Molly-M-Laugh/Senior-Final/Hardware/Final Circuits/sd_pcm.pdf

Choosing a Protection Circuit Module for a One-Cell Lithium Iron Phosphate Battery For this project, I am using a one-cell lithium iron phosphate battery, so I am choosing a protection circuit module (often called a protection board) instead of a full battery management system. I chose a protection circuit module because a one-cell battery does not need cell balancing, which is one of the main functions of a larger battery management system used in multi-cell battery packs. In many online listings, sellers still call one-cell protection boards “battery management systems,” but for my design the more accurate term is protection circuit module.
A protection circuit module is the board that sits between the battery and the rest of the system and protects the battery during unsafe conditions, such as overcharging, over-discharging, over-current, and short circuits.

What I need to check when choosing a protection circuit module
1) It must match the battery chemistry and cell count
The most important thing is that the board must be made for a one-cell lithium iron phosphate battery. This is usually written as 1S LiFePO4.
This must be checked first because lithium iron phosphate batteries use different voltage limits than regular lithium-ion or lithium-polymer batteries.
When looking at the datasheets, look for wording like:
- 1S LiFePO4
- one-cell lithium iron phosphate protection board
- LiFePO4 protection circuit module
2) The continuous discharge current rating must be high enough
The protection circuit module has a continuous discharge current rating, which determines how much current it can safely pass during normal operation without overheating or tripping.
This matters because the system will draw current from the battery through this board, and the board must be able to handle that current comfortably. Even though my first-pass estimate for peak battery current is around the 1 amp range, I should still choose a board with margin because startup behavior, converter bursts, and real-world conditions can cause temporary increases.
For my prototype, a practical choice is:
- at least 3 amps continuous discharge current
- 5 amps continuous is even better because it gives extra margin and reduces the chance of nuisance trips
3) Check the over-current protection behavior
Besides the continuous rating, the board usually has an over-current protection threshold, which is the current level where it decides something is wrong and shuts off or trips protection.
This value is important because I do not want the board to trip during normal system operation, but I do want it to trip if there is a real fault. If the threshold is too low, the system may randomly shut off during startup or current bursts. If the threshold is too high, the protection may be less effective.
I should also check whether the listing mentions short-circuit protection, since that is another major job of the protection circuit module.
4) The charge current rating must support the charger
Even though my design will not charge while running, the protection circuit module still has to handle charging current when I do charge the battery.
I need to check the board’s maximum charge current and make sure it is at least as high as the charging current I plan to use. If the charger current is too high for the protection board, the board can overheat or trip unexpectedly during charging.
This is one reason it helps to decide my charger current target early (for example, 0.5 amp, 1 amp, etc.), even before finalizing the charger part number.
5) Confirm the built-in protection thresholds are compatible with a lithium iron phosphate cell

The protection circuit module will have built-in voltage thresholds for battery protection and verify they make sense for a one-cell lithium iron phosphate battery.
The values that need to be checked (if listed) are:
- over-voltage protection threshold and release threshold
- under-voltage protection threshold and release threshold
The main idea is that these values should be appropriate for the battery chemistry and should not conflict with the charger or with normal system operation.
6) Check the quiescent current (standby drain)
The protection circuit module draws a small amount of current from the battery even when the system is off. This is usually called quiescent current, standby current, or current consumption.
This matters because if the device sits unused for a long time, the protection board itself can slowly drain the battery. For a prototype, this may not be the top priority, but it is still worth checking and comparing if multiple boards are available.
Lower quiescent current is generally better.
7) Check the wiring style and connection ports
Protection boards are not all wired the same way, so make sure to understand the board’s connection style before buying.
Some boards use a common port arrangement, where charging and discharging share the same output negative terminal. Other boards use separate charge and discharge ports. Because my system will not charge while running, a common-port one-cell lithium iron phosphate protection board is usually a simpler and perfectly reasonable option. Before buying, make sure the datasheet includes a clear wiring diagram and clear terminal labels, such as:
- battery positive
- battery negative
- pack/output positive

- pack/output negative
Good labeling reduces wiring mistakes, which are especially dangerous with battery circuits.
8) Check the physical size and mechanical fit
Since this is a wearable project, the protection board must fit physically in the layout and be easy to secure safely.
I should check:
- board dimensions (length and width)
- thickness / tall components
- whether the solder pads are large enough for the wire gauge I plan to use
- whether I can insulate it and mount it securely in a pouch or enclosure
Even if a board is electrically perfect, it is a poor choice if it is too large, mechanically fragile, or difficult to wire in a wearable system.
9) Temperature protection is a useful bonus feature
Some protection circuit modules include temperature protection or support an external thermistor input. Many simple low-cost boards do not.
This feature is not always required for a first prototype, but it is helpful because batteries should not be charged or discharged outside safe temperature ranges. Since the device is wearable, temperature-related safety features are a nice improvement if I can find a board with clear documentation.
10) Check how the board recovers after a fault
Different protection boards recover differently after an over-current or short-circuit trip. Some boards recover automatically after the fault is removed, while others require a charger connection or a power reset before they start working again.
This matters for usability and testing. In a prototype, automatic recovery can be much easier to work with because it reduces debugging confusion after a temporary fault.

11) Prioritize boards with real documentation
A lot of low-cost battery protection boards are sold with almost no useful specifications. Because this is a battery-related part, I should prefer boards that include real technical information.
The best listings or datasheets will include:
- clear chemistry and cell count (must say one-cell lithium iron phosphate)
- current ratings (continuous charge and discharge)
- protection thresholds (or at least some threshold information)
- wiring diagram or terminal labels
- board dimensions

What information I need from my own design before choosing the board
To choose the protection circuit module correctly, I need a few inputs from my battery and system design.
From the battery datasheet, I need:
- battery chemistry (lithium iron phosphate)
- one-cell configuration
- charge voltage
- discharge limits
- maximum continuous discharge current
From my system estimate, I need:
- estimated peak battery current (because this drives the protection board current rating)
- estimated average battery current (less critical for protection board sizing, but useful for overall power planning)
From my charging plan, I need:

- intended charger current

Practical protection circuit module target for my project
For this prototype, a good practical target is to choose a protection circuit module that is:
- one-cell lithium iron phosphate (1S LiFePO4)
- rated for at least 3 amps continuous discharge current
- preferably 5 amps continuous discharge current for extra margin
- able to support my planned charge current
- includes over-current and short-circuit protection
- has clear wiring labels and a wiring diagram
- physically small enough for my wearable layout

Final note: protection circuit module versus charger
A protection circuit module does not charge the battery by itself. It only protects the battery.
That means a separate lithium iron phosphate charger (or a combined charger-plus-protection solution) is still needed for later in the design.

Chosen PCM: Protection Circuit Module (PCB) for 1 cell (3.2V) LiFePO4 Battery Pack at 5A limited (#481)
