Molly-M-Laugh/Senior-Final/Hardware/Circuits and PCB related/INA3221 BRreakout.jpg

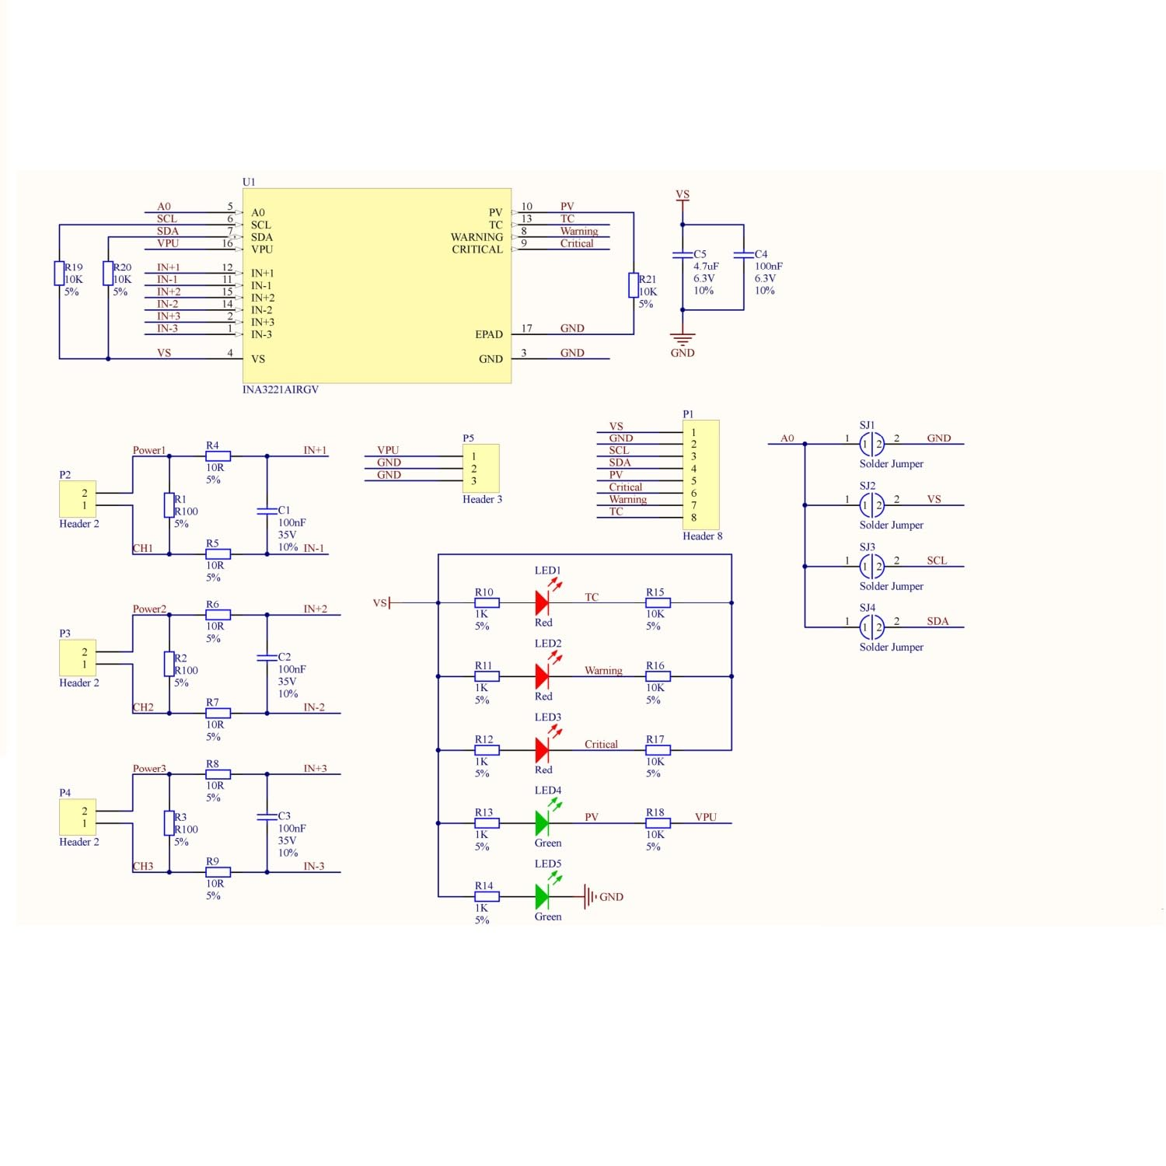
Hardware/Circuits and PCB related/INA3221 BRreakout.jpg
