Molly-M-Laugh/Senior-Final/Hardware/Circuits and PCB related/STM32F103C8T6-Blue-Pill-schematic-diagram.png

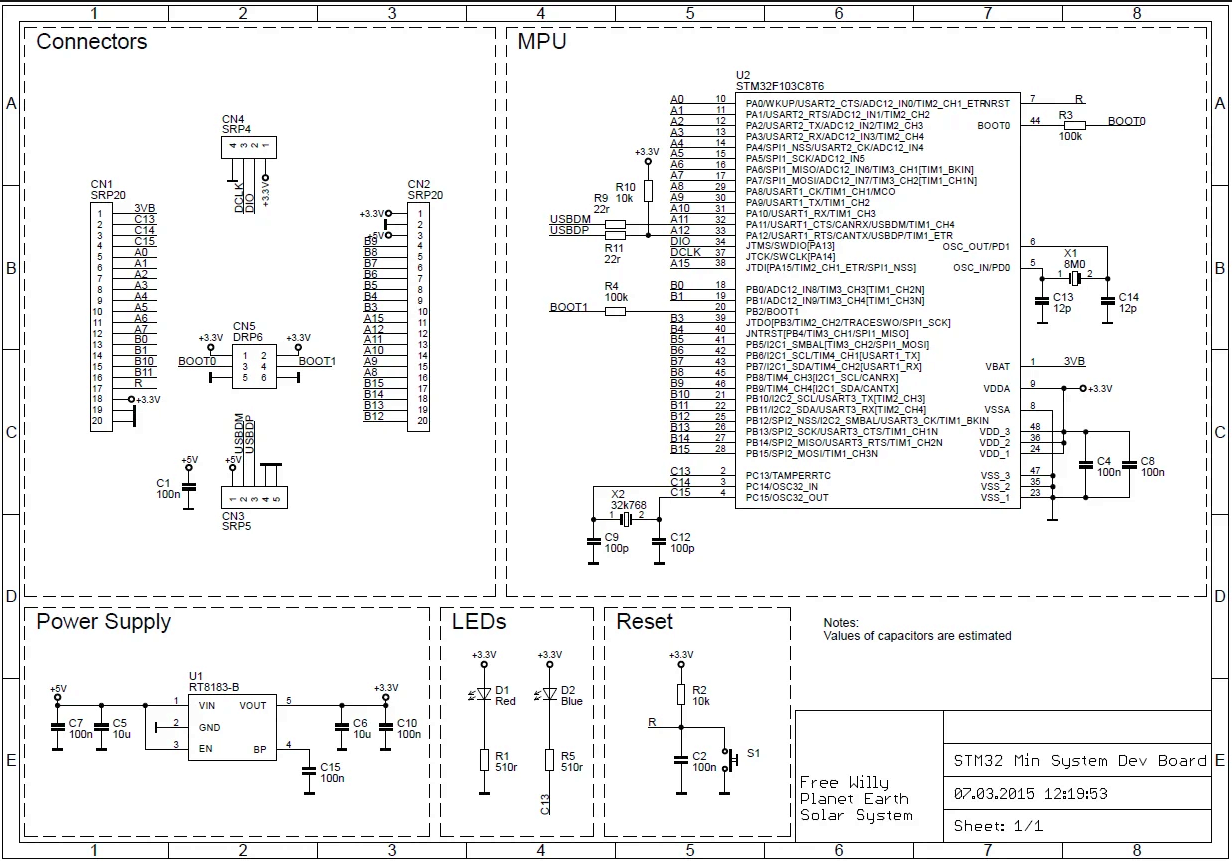
Hardware/Circuits and PCB related/STM32F103C8T6-Blue-Pill-schematic-diagram.png
