Molly-M-Laugh/Senior-Final/Hardware/Circuits and PCB related/STM32F103C8T6-pinout-diagram.jpg

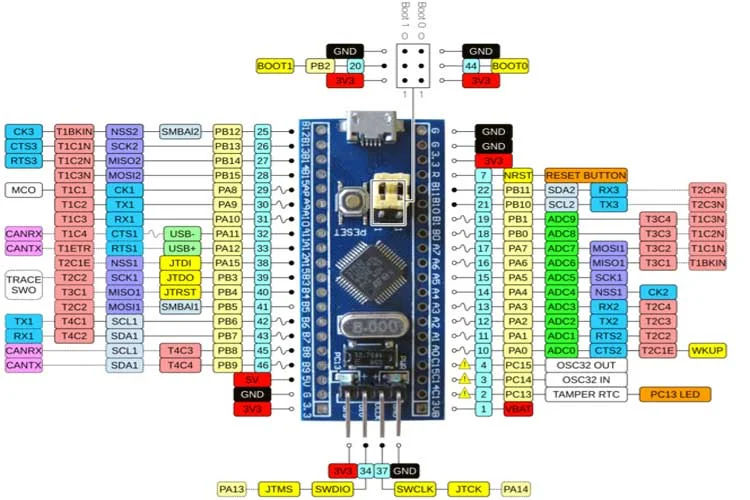
Hardware/Circuits and PCB related/STM32F103C8T6-pinout-diagram.jpg
