Molly-M-Laugh/Senior-Final/Hardware/Fabric Designs/DesignV1.JPG

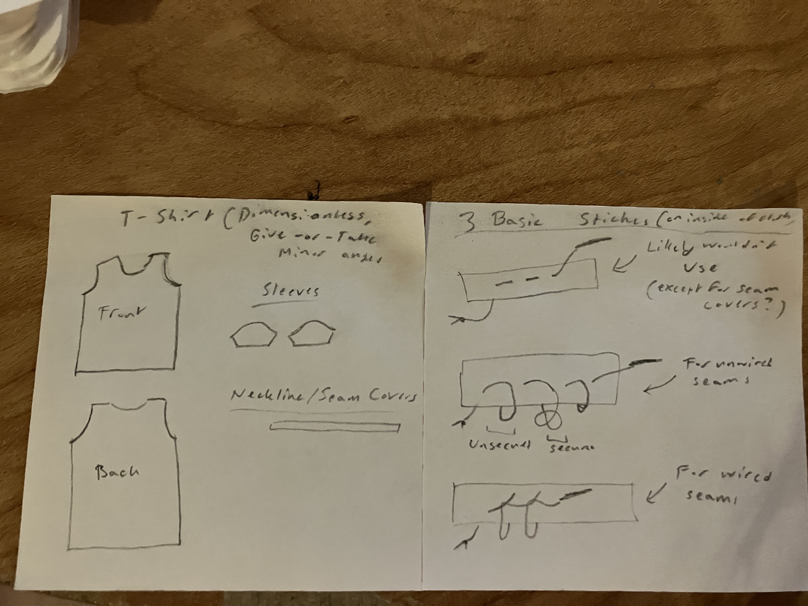
Hardware/Fabric Designs/DesignV1.JPG
