Molly-M-Laugh/Senior-Final/Hardware/Fabric Designs/DesignV2.JPG

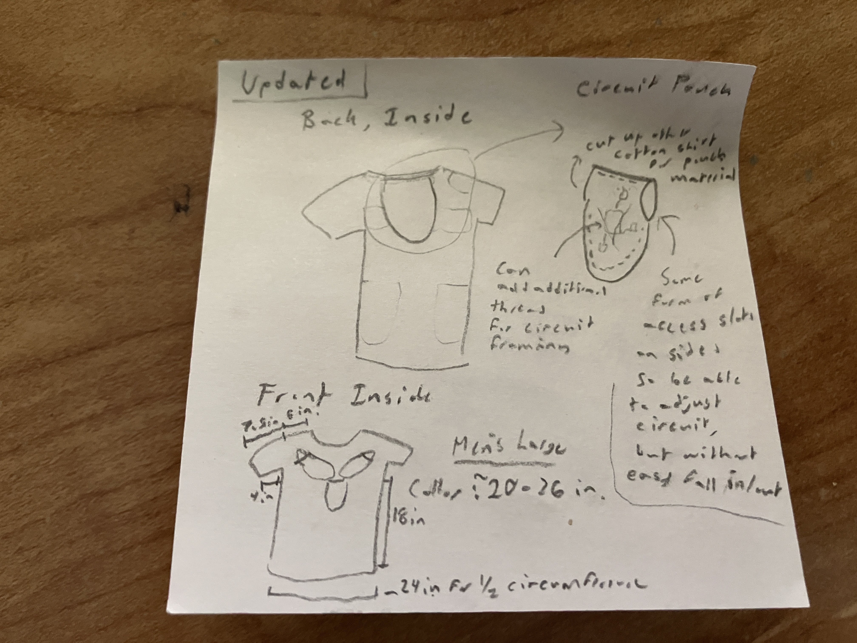
Hardware/Fabric Designs/DesignV2.JPG
