Molly-M-Laugh/Senior-Final/Hardware/Fabric Designs/serger_example.jpg

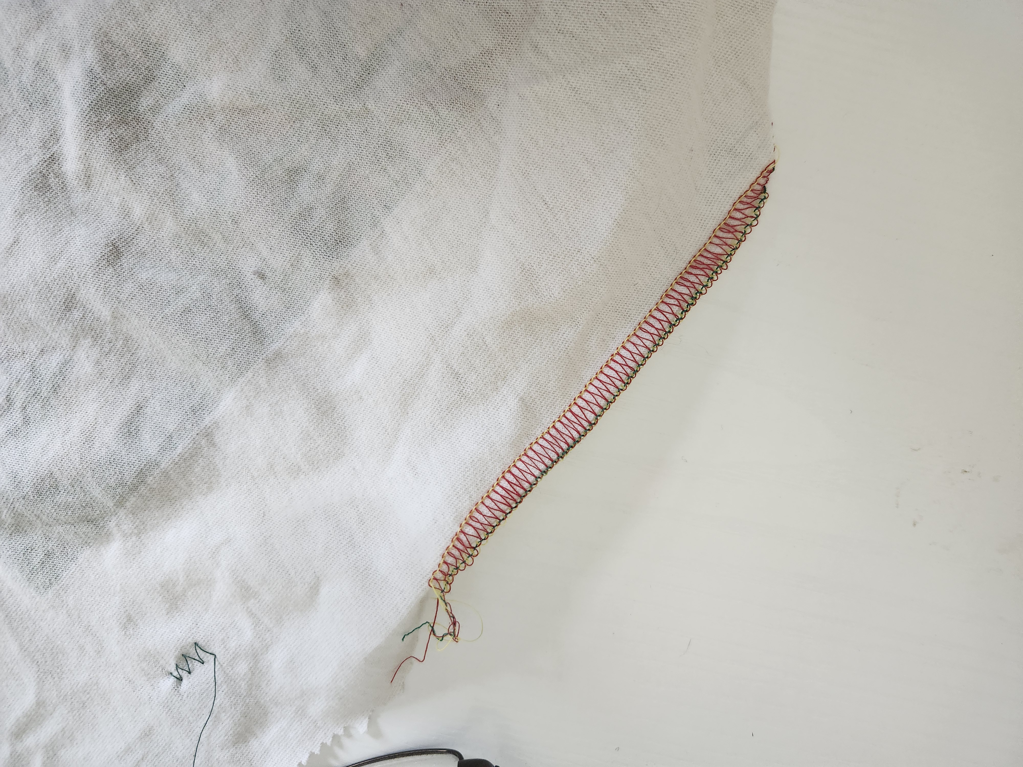
Hardware/Fabric Designs/serger_example.jpg
