Molly-M-Laugh/Senior-Final/Hardware/Fabric Designs/Sewing Knot.JPG

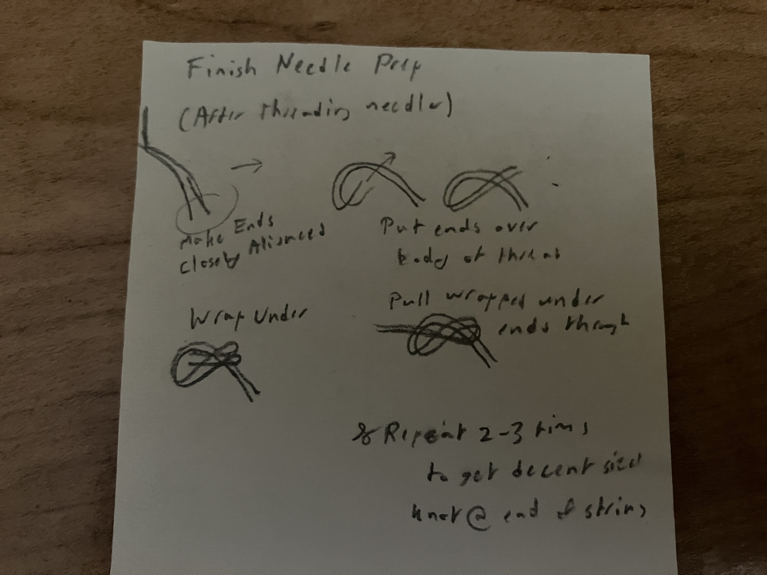
Hardware/Fabric Designs/Sewing Knot.JPG
