Molly-M-Laugh/Senior-Final/Hardware/Fabric Designs/sewing_machine_setting.jpg

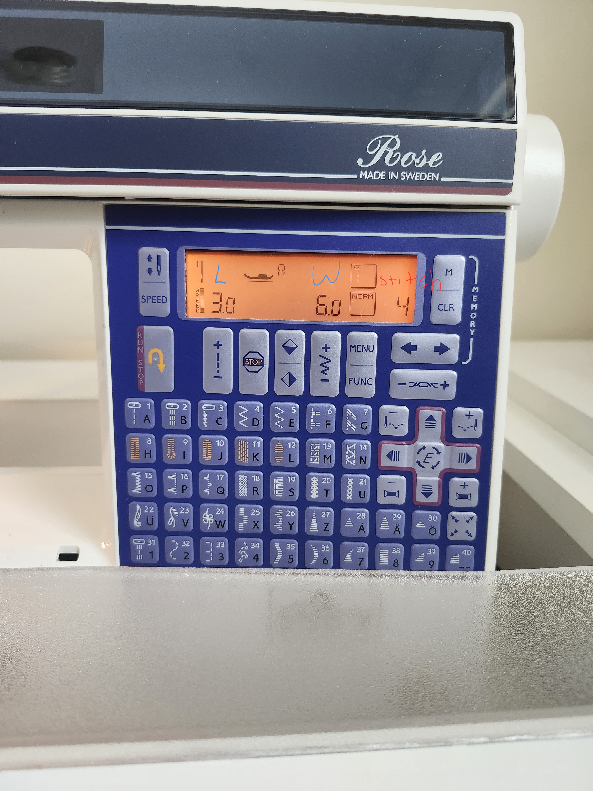
Hardware/Fabric Designs/sewing_machine_setting.jpg
