Molly-M-Laugh/Senior-Final/Hardware/Fabric Designs/Stitch_settings.jpg

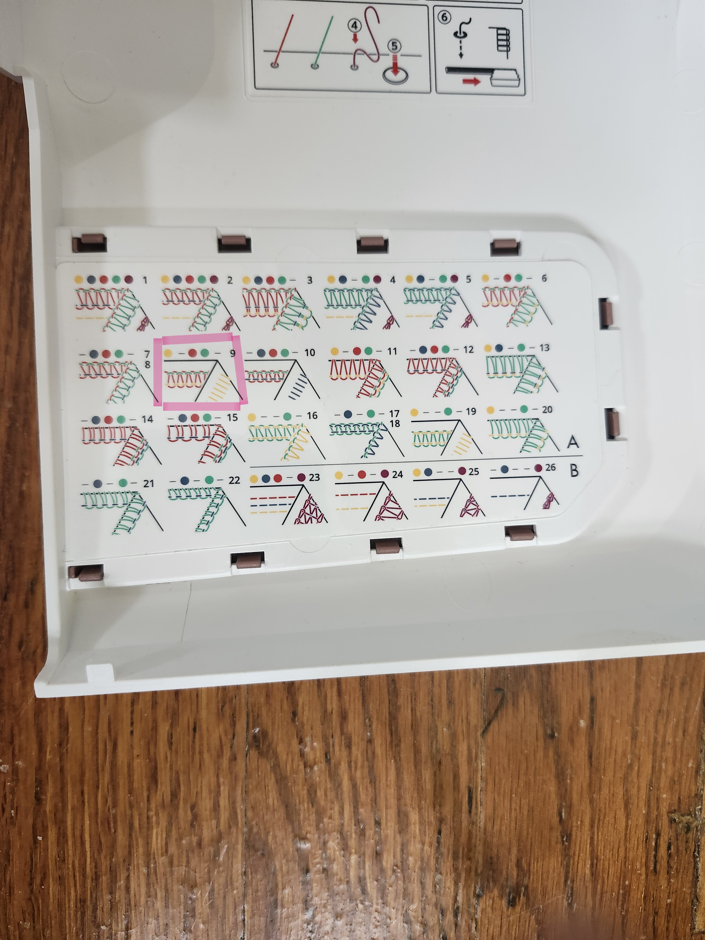
Hardware/Fabric Designs/Stitch_settings.jpg
