Molly-M-Laugh/Senior-Final/inital placement.png

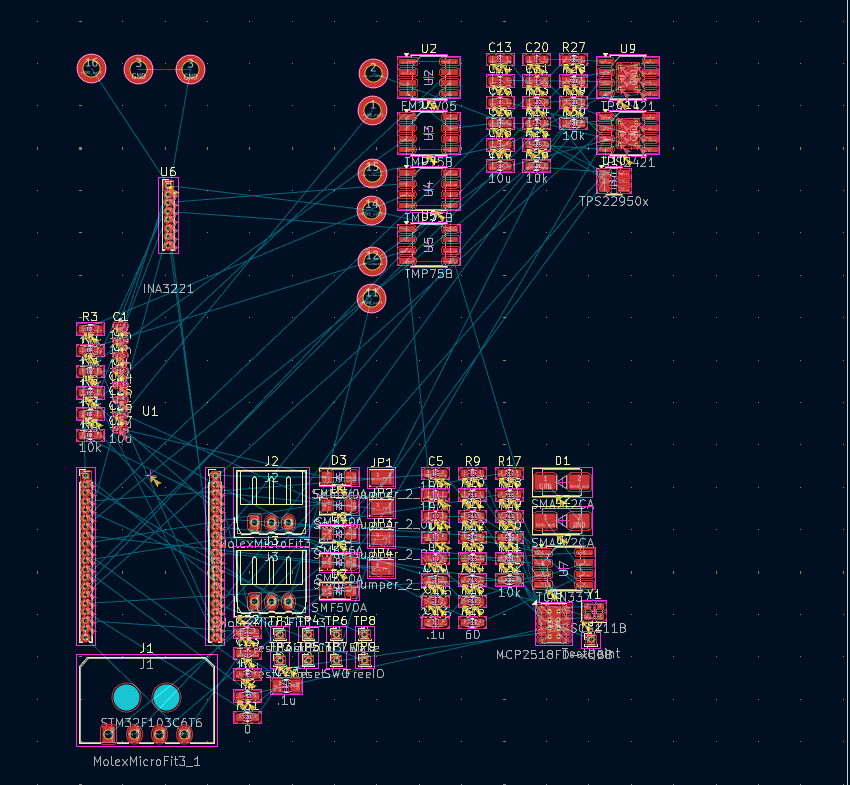
inital placement.png
