Molly-M-Laugh/Senior-Final/PCB_layer_B.png

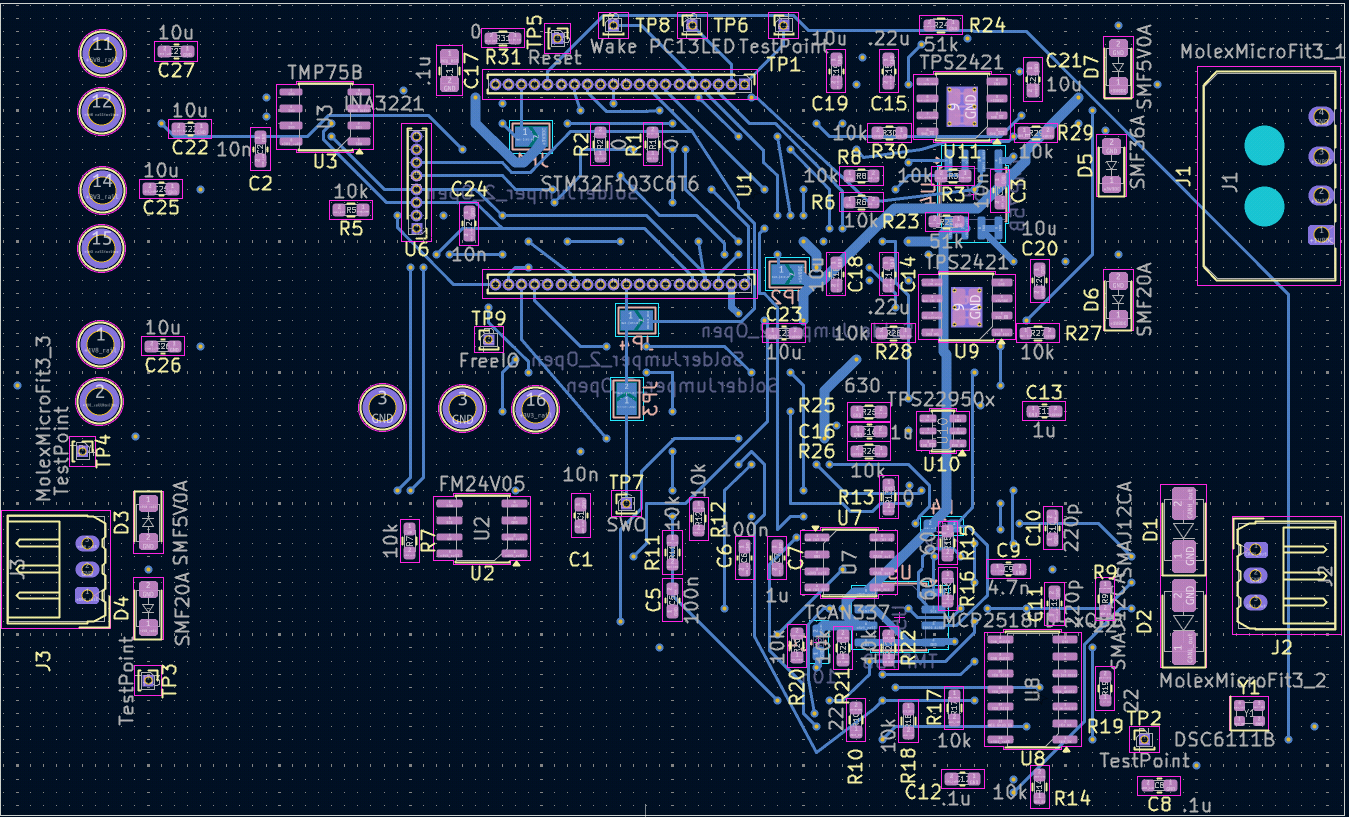
PCB_layer_B.png
