Molly-M-Laugh/Senior-Final/PCB_layer_F.png

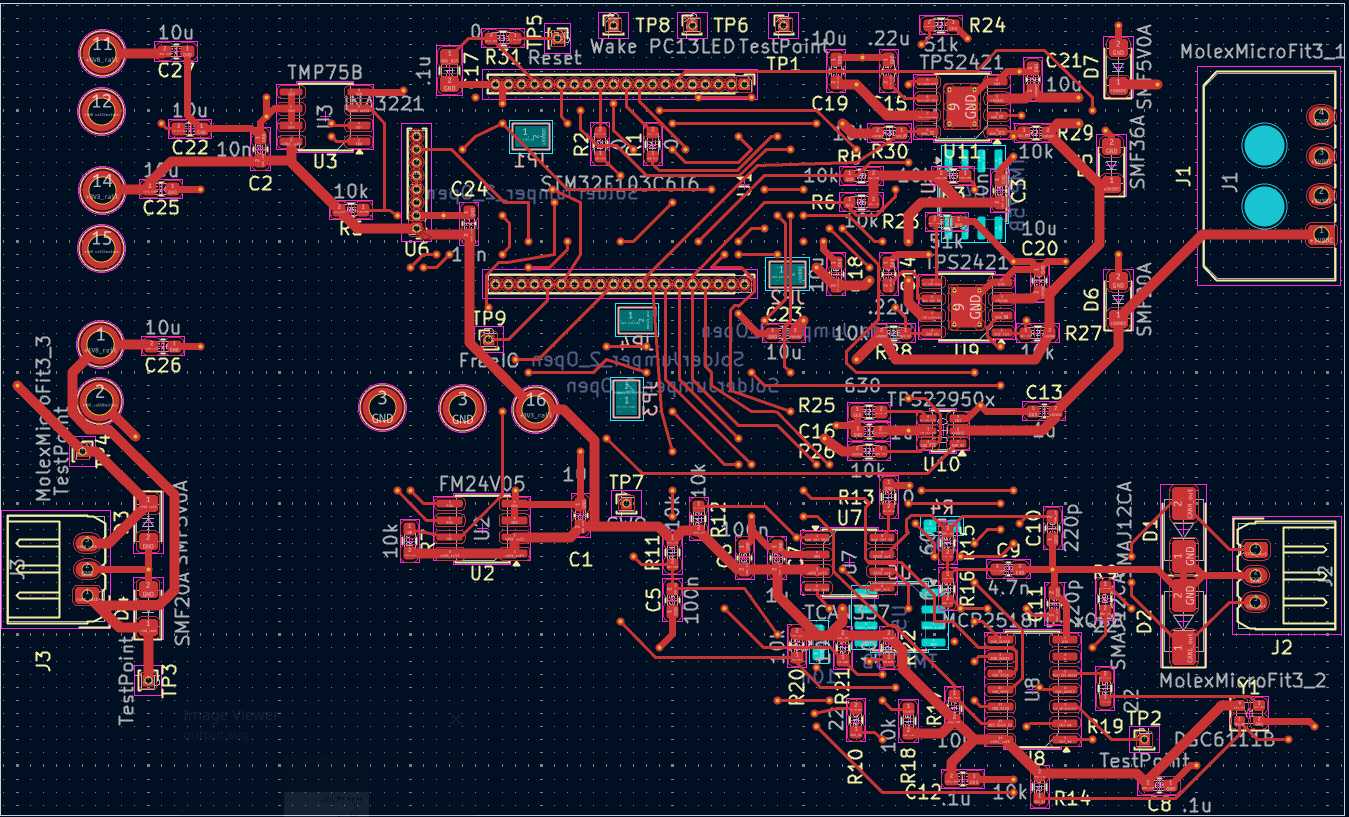
PCB_layer_F.png
