Molly-M-Laugh/Senior-Final/PCB_layer_In1.png

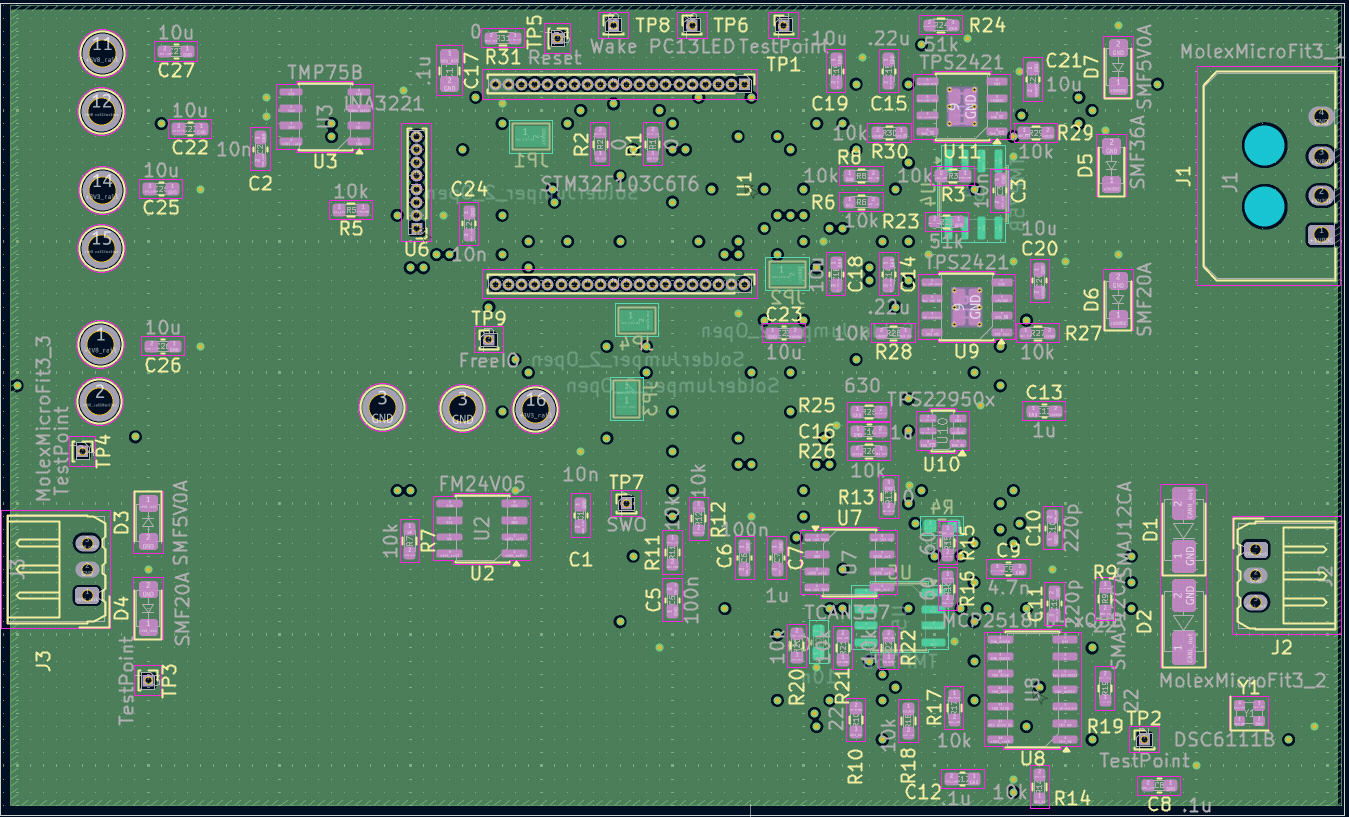
PCB_layer_In1.png
