Molly-M-Laugh/Senior-Final/PCB_layer_In2.png

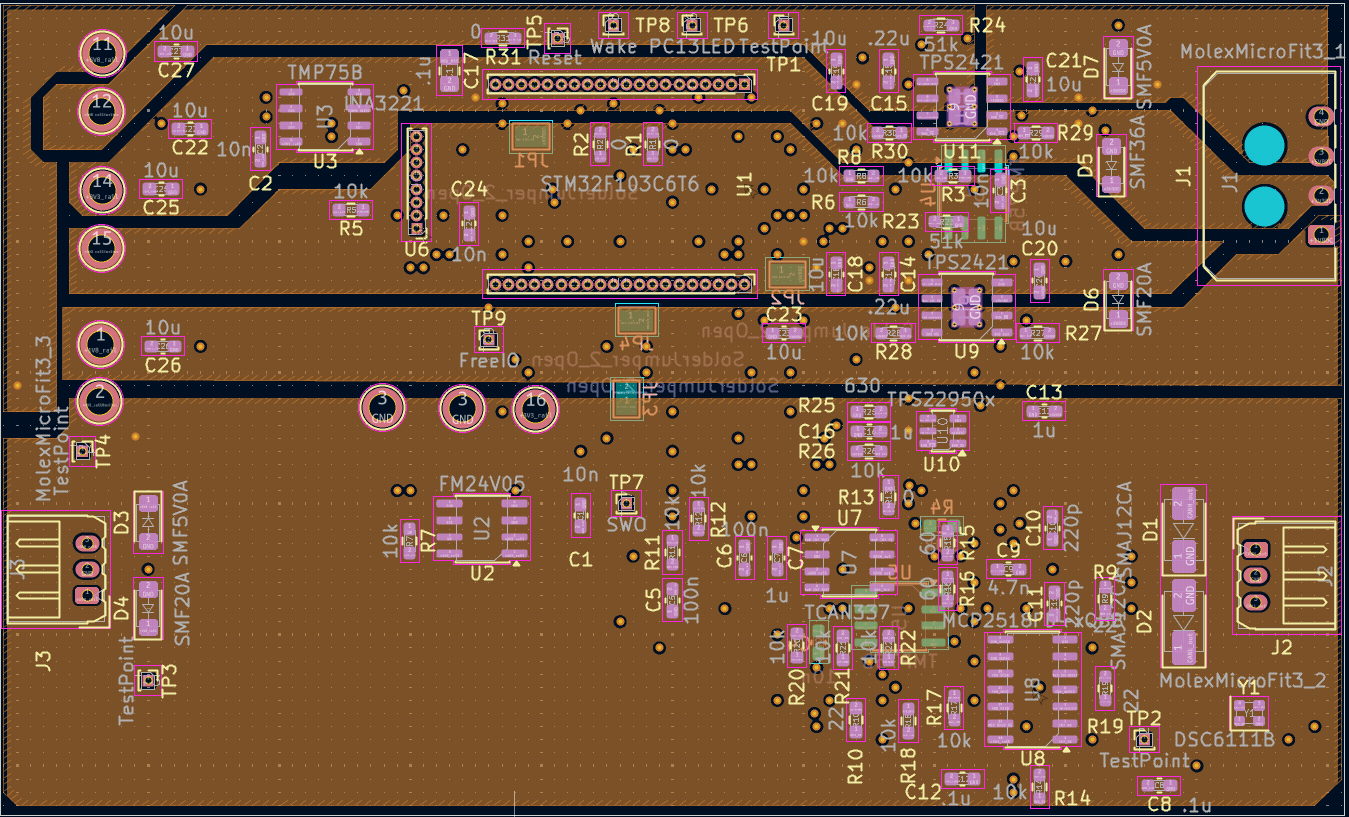
PCB_layer_In2.png
