Molly-M-Laugh/Senior-Final/PCB_Render_Bottom.png

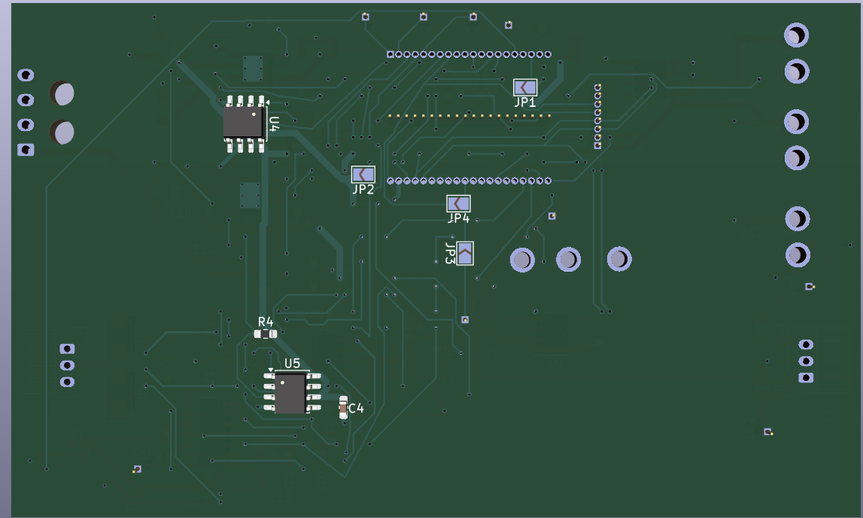
PCB_Render_Bottom.png
