Molly-M-Laugh/Senior-Final/PCB_Render_Top.png

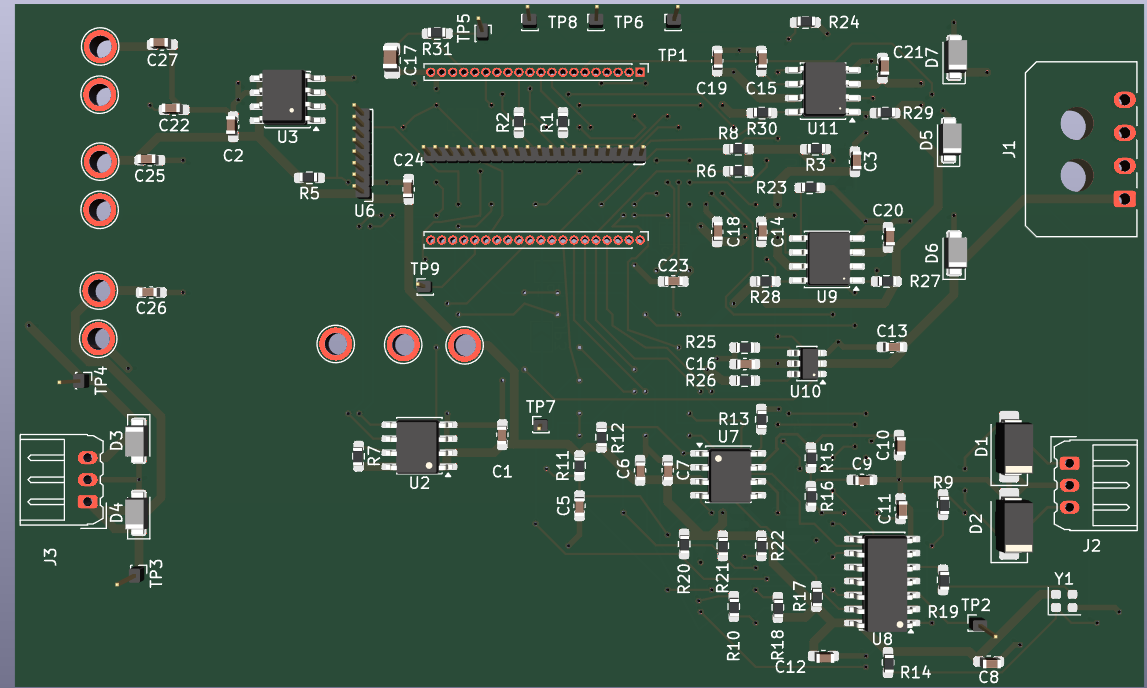
PCB_Render_Top.png
