Molly-M-Laugh/Senior-Final/Hardware/Fabric Designs/Seam Guide.JPG

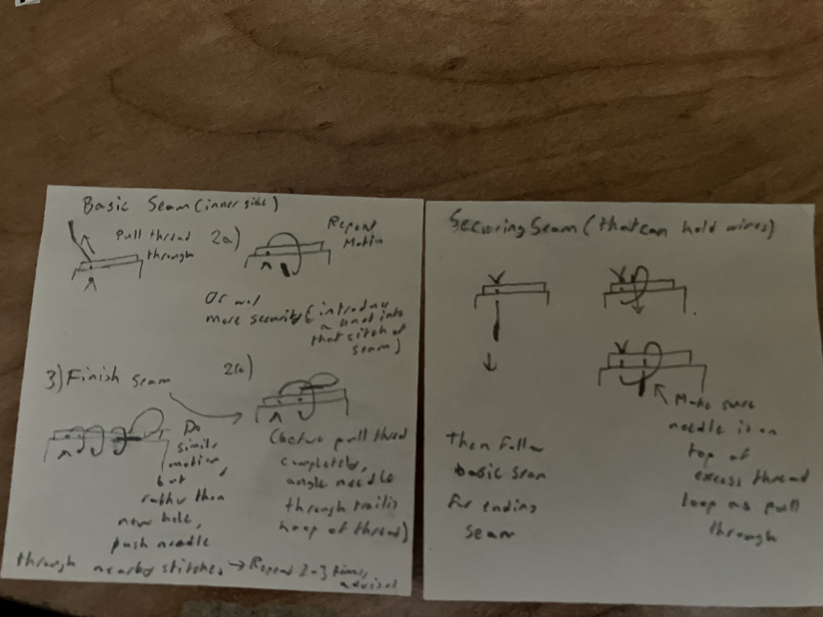
Hardware/Fabric Designs/Seam Guide.JPG
