Molly-M-Laugh/Senior-Final/Hardware/Fabric Designs/SewingM_Step_Drawings.JPG

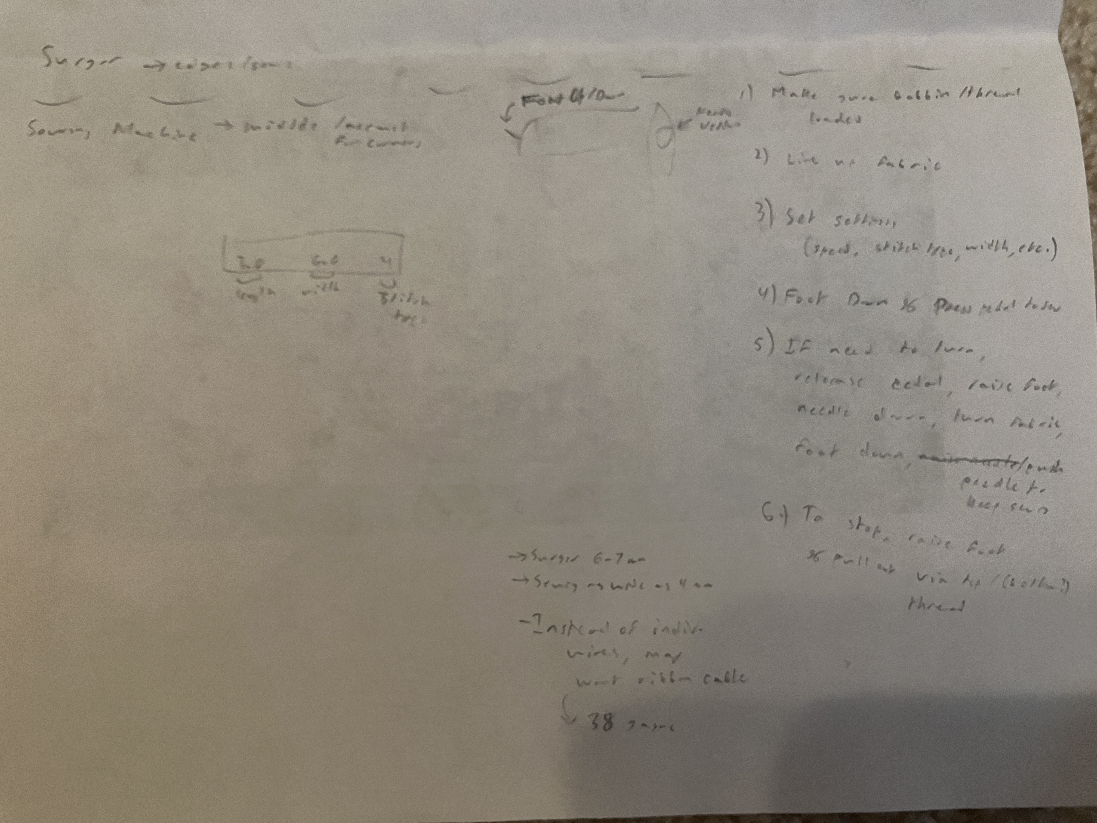
Hardware/Fabric Designs/SewingM_Step_Drawings.JPG
