Molly-M-Laugh/Senior-Final/Hardware/Fabric Designs/Surger_Step_Drawings.JPG

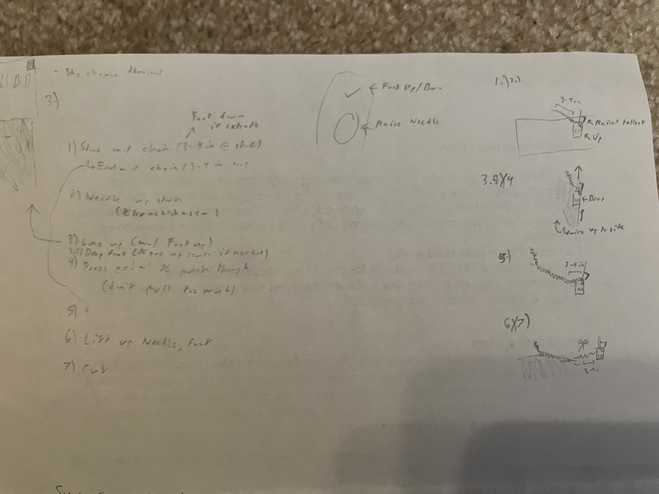
Hardware/Fabric Designs/Surger_Step_Drawings.JPG
