Molly-M-Laugh/Senior-Final/Hardware/Fabric Designs/Outer Seam Result.JPG

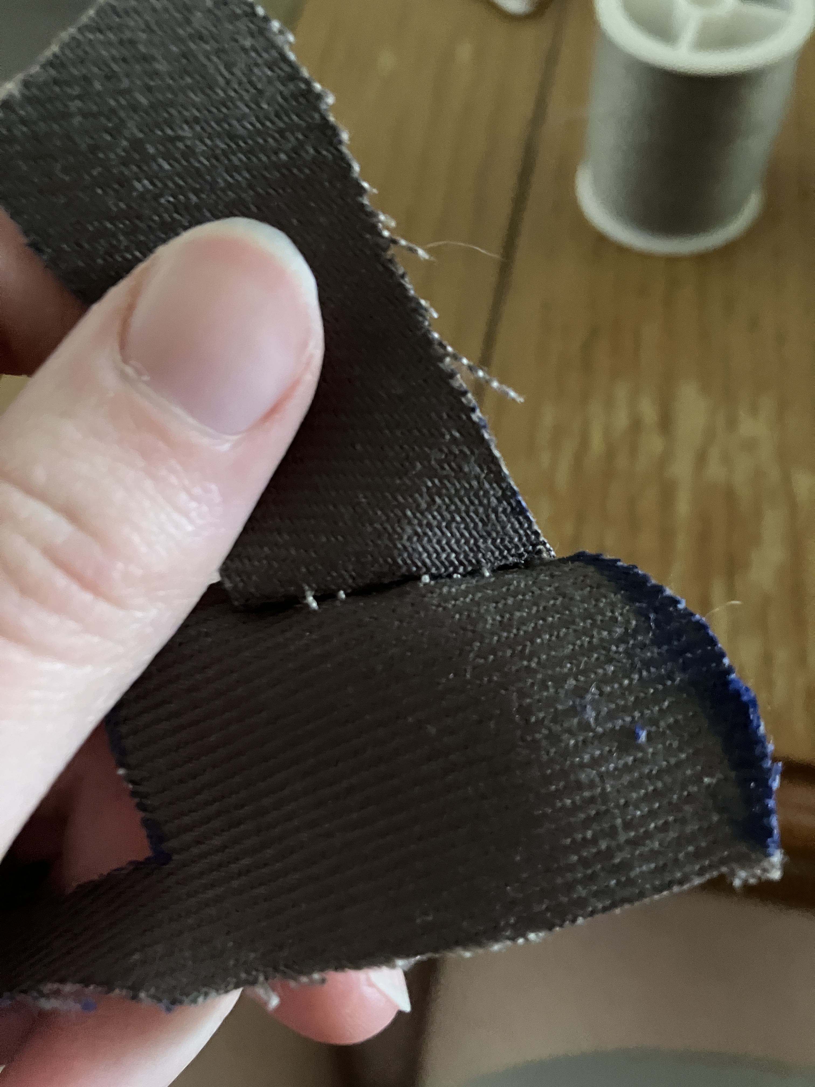
Hardware/Fabric Designs/Outer Seam Result.JPG
