Molly-M-Laugh/Senior-Final/Hardware/Final Circuits/Cell Supervisor_rev1.pdf

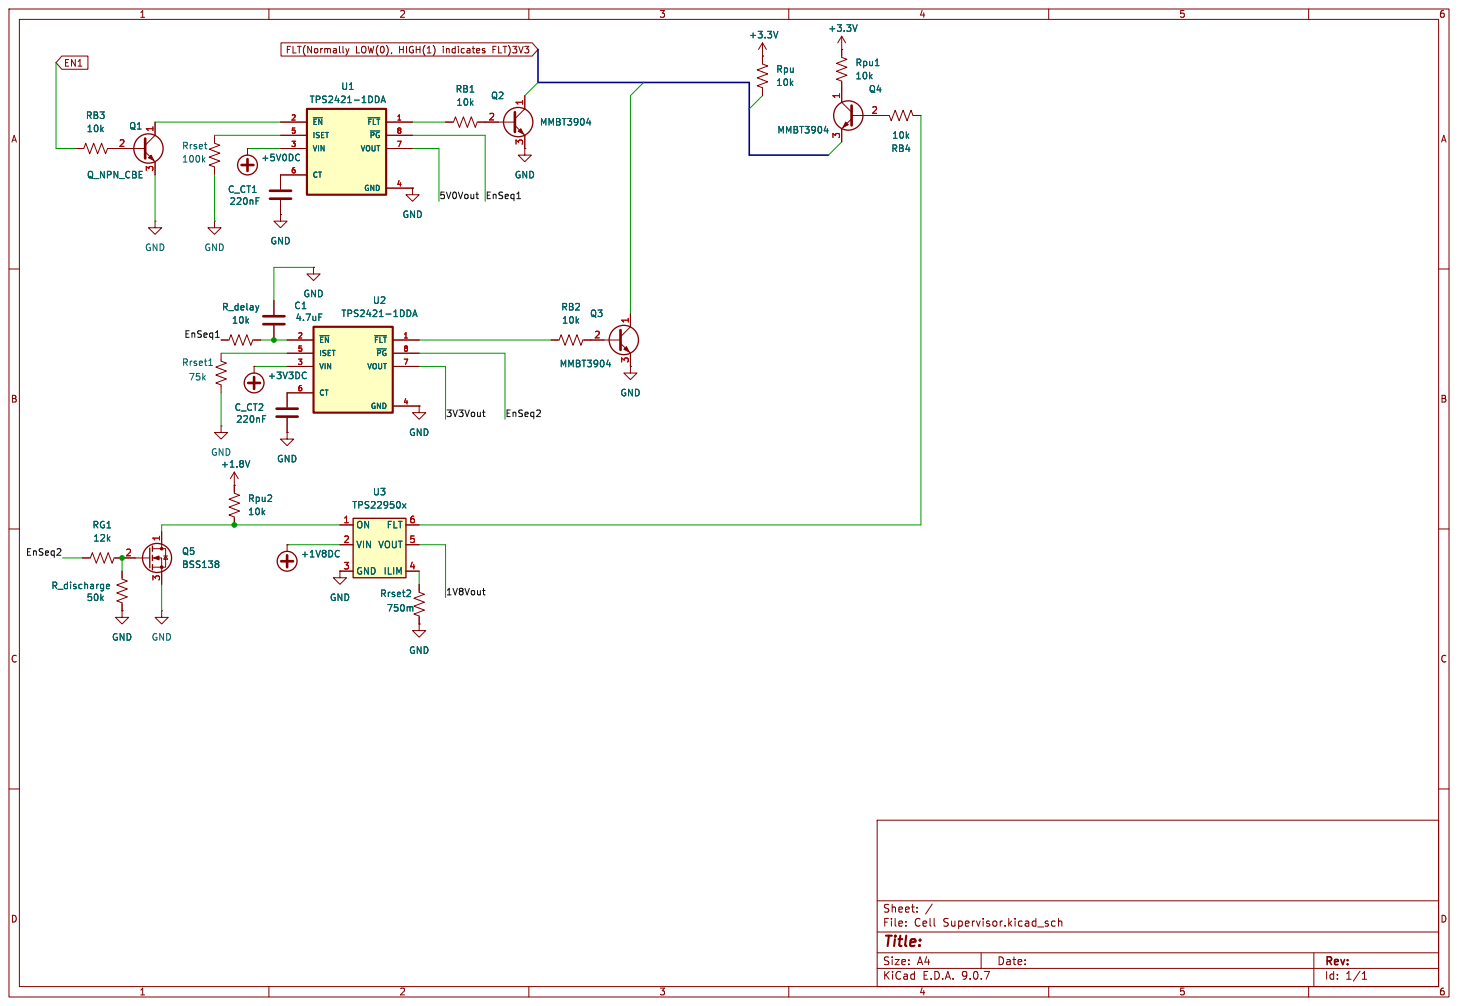
[picture p32: page 1]

1 3 Q5 BSS138 GND GND GND GND ON 1 VIN 2 GND 3 FLT 6 VOUT 5

Id: 1/1 Title: File: Cell Supervisor.kicad_sch Sheet: / Rrset2
