Molly-M-Laugh/Senior-Final/Hardware/Fabric Designs/sewing_machine_example.jpg

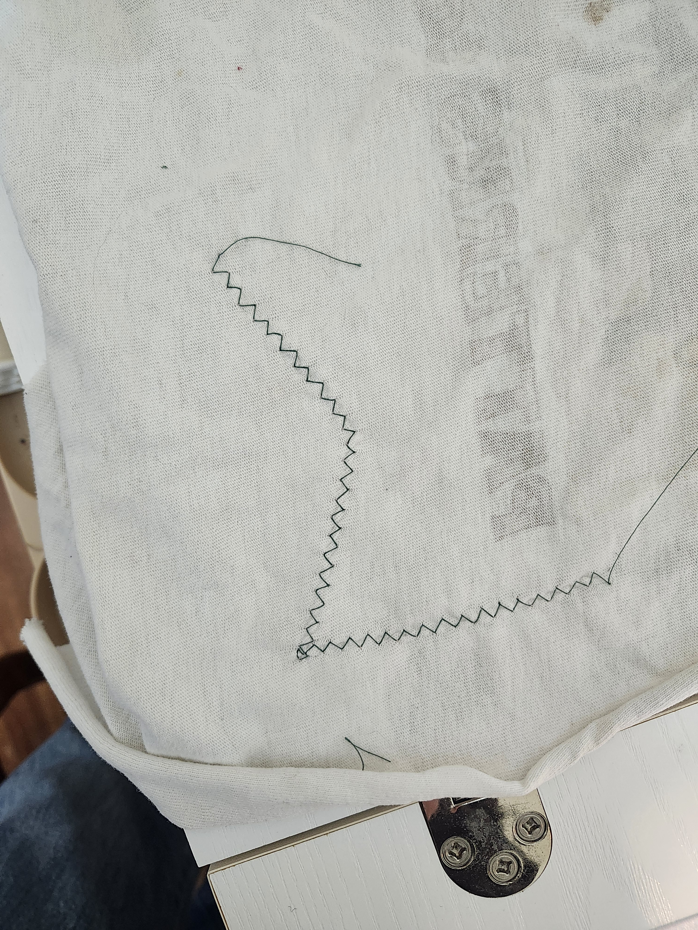
Hardware/Fabric Designs/sewing_machine_example.jpg
