Molly-M-Laugh/Senior-Final/Hardware/Fabric Designs/Surger_Printout.JPG

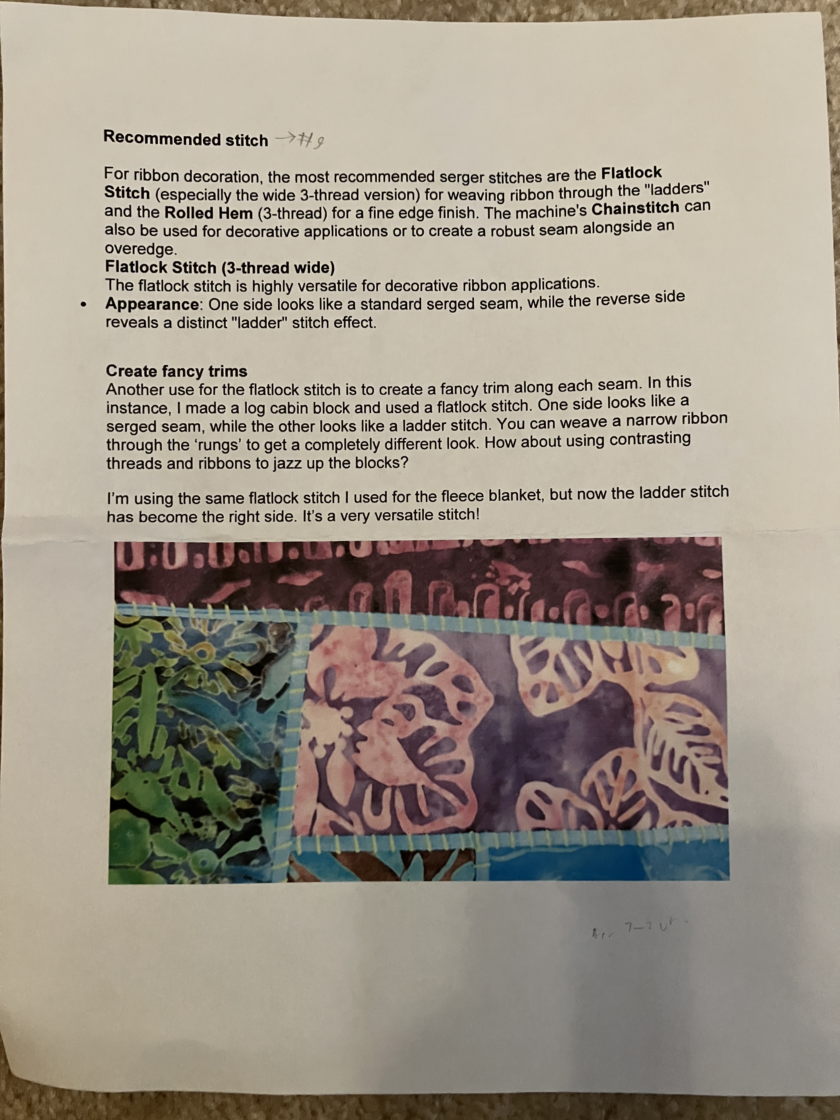
Hardware/Fabric Designs/Surger_Printout.JPG
