Molly-M-Laugh/Senior-Final/Hardware/Fabric Designs/Inner Seam Result.JPG

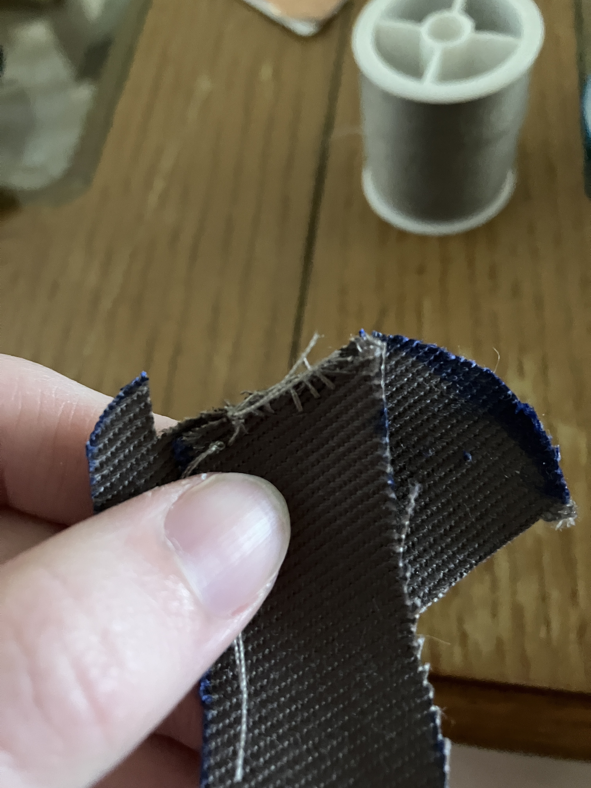
Hardware/Fabric Designs/Inner Seam Result.JPG
